LafeLabs/switchotron/switchotron-3buttons-3lights/eagle-screenshot.png

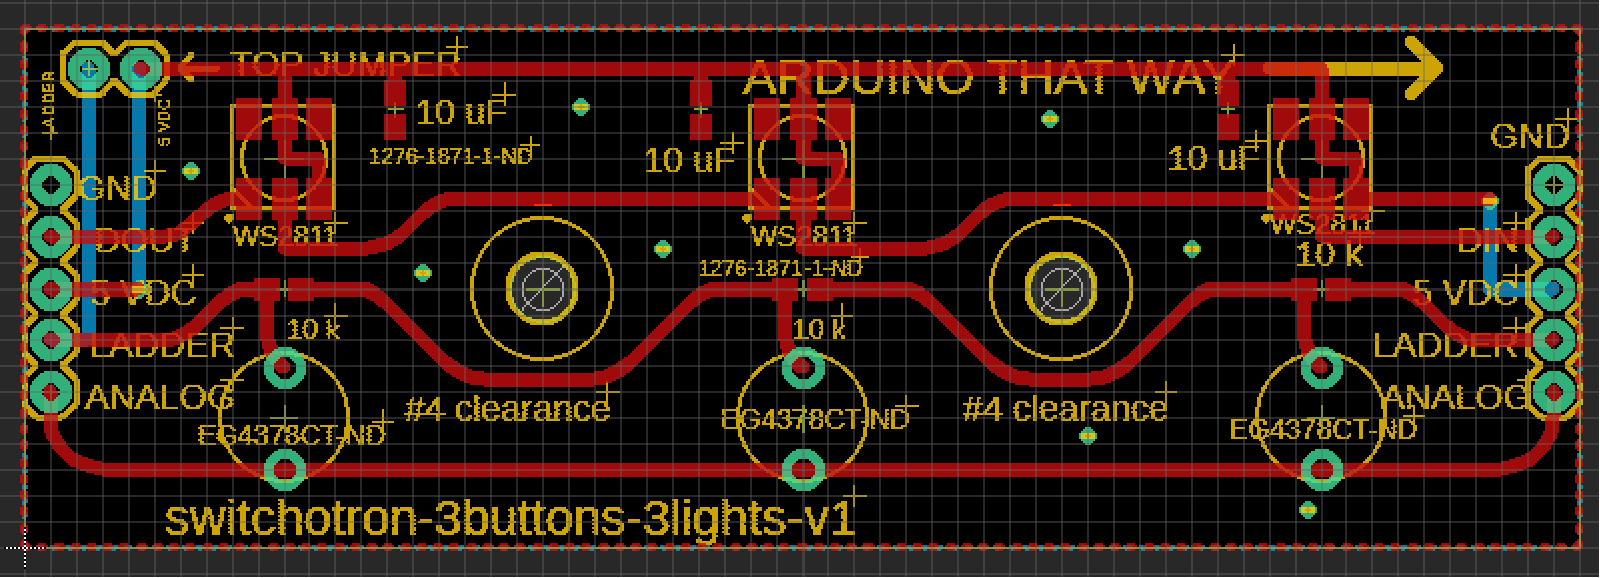
switchotron-3buttons-3lights/eagle-screenshot.png
