LafeLabs/switchotron/switchotron-3buttons-3lights/gerber-top-screenshot-v2.png

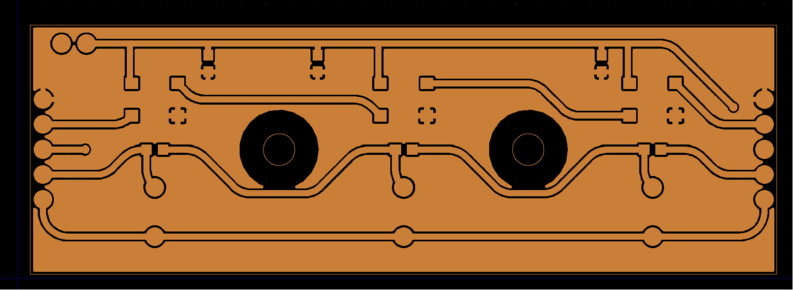
switchotron-3buttons-3lights/gerber-top-screenshot-v2.png
