LafeLabs/switchotron/switchotron-relayboard/relayboard-kit-photo.png

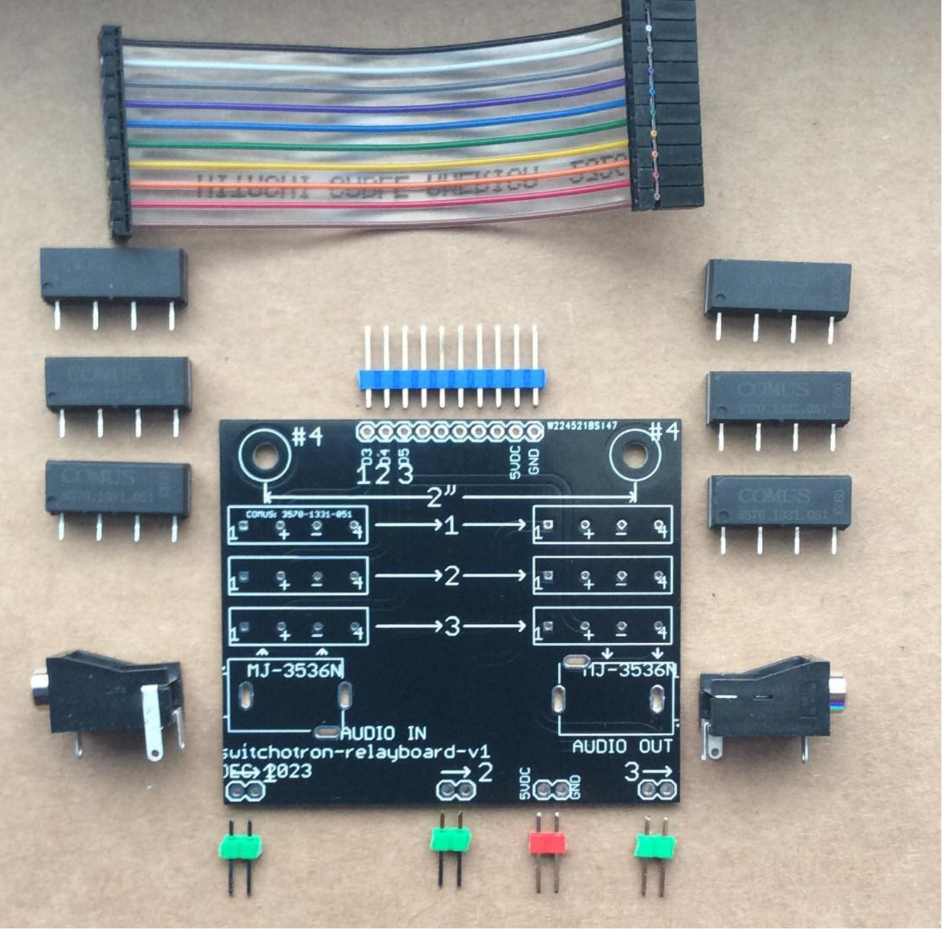
switchotron-relayboard/relayboard-kit-photo.png
