LafeLabs/switchotron/topology/signal1.png

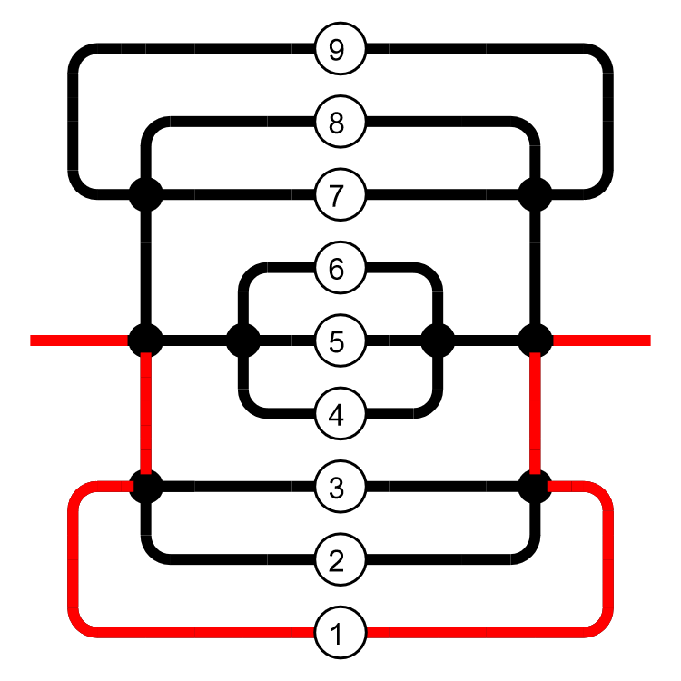
topology/signal1.png
