LafeLabs/switchotron/topology/signal2.png

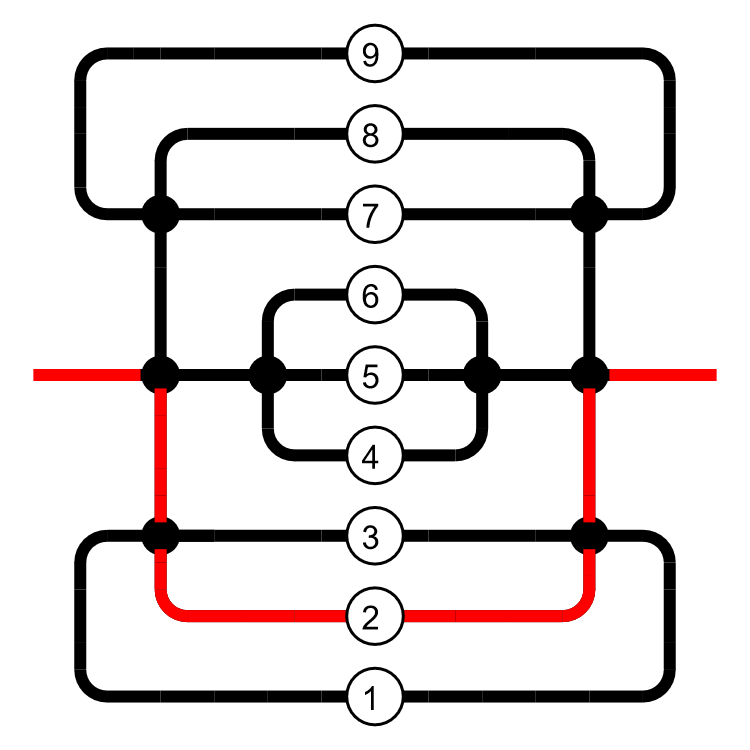
topology/signal2.png
