LafeLabs/switchotron/switchotron-3buttons-3lights/kicad/3buttons-3lights-kicad/3buttons-3lights-kicad.kicad_pcb

## KiCad design schematic/8251_Arduino.kicad_sch

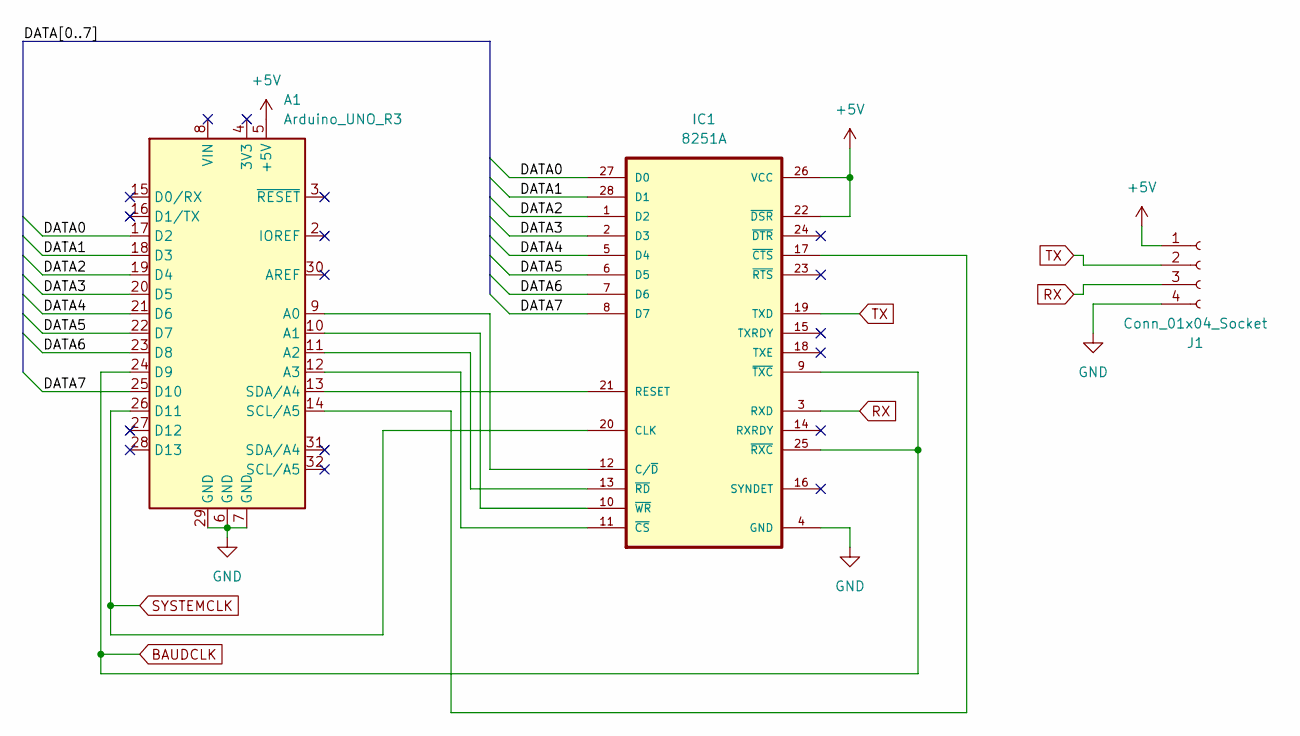
[picture p26: schematic 8251_Arduino.kicad_sch]

Parts:
A1: Arduino_UNO_R3
IC1: 8251A; DIL28-6
J1: Conn_01x04_Socket

Connections:
+5V: A1.5 (+5V), IC1.22 (~DSR), IC1.26 (VCC), J1.1
BAUDCLK: A1.24 (D9), IC1.9 (~TXC), IC1.25 (~RXC)
DATA0: A1.17 (D2), IC1.27 (D0)
DATA1: A1.18 (D3), IC1.28 (D1)
DATA2: A1.19 (D4), IC1.1 (D2)
DATA3: A1.20 (D5), IC1.2 (D3)
DATA4: A1.21 (D6), IC1.5 (D4)
DATA5: A1.22 (D7), IC1.6 (D5)
DATA6: A1.23 (D8), IC1.7 (D6)
DATA7: A1.25 (D10), IC1.8 (D7)
GND: A1.6 (GND), A1.7 (GND), A1.29 (GND), IC1.4 (GND), J1.4
unnamed: A1.9 (A0), IC1.12 (C/~D)
unnamed: A1.10 (A1), IC1.10 (~WR)
unnamed: A1.11 (A2), IC1.13 (~RD)
unnamed: A1.12 (A3), IC1.11 (~CS)
unnamed: A1.13 (SDA/A4), IC1.21 (RESET)
unnamed: A1.14 (SCL/A5), IC1.17 (~CTS)
RX: IC1.3 (RXD), J1.3
SYSTEMCLK: A1.26 (D11), IC1.20 (CLK)
TX: IC1.19 (TXD), J1.2
